justinjradi/smooth-scrolling-mouse/mouse-firmware-2/Core/Inc/board_api.h

/*
 * The MIT License (MIT)
 *
 * Copyright (c) 2019 Ha Thach (tinyusb.org)
 *
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
 * This file is part of the TinyUSB stack.
 */

#ifndef _BOARD_API_H_
#define _BOARD_API_H_

#ifdef __cplusplus
extern "C" {
#endif

#include <stdint.h>
#include <inttypes.h>
#include <stdbool.h>
#include <string.h>

#include "tusb.h"

#if CFG_TUSB_OS == OPT_OS_FREERTOS
#if TUP_MCU_ESPRESSIF
  // ESP-IDF need "freertos/" prefix in include path.
  // CFG_TUSB_OS_INC_PATH should be defined accordingly.
  #include "freertos/FreeRTOS.h"
  #include "freertos/semphr.h"
  #include "freertos/queue.h"
  #include "freertos/task.h"
  #include "freertos/timers.h"
#else
  #include "FreeRTOS.h"
  #include "semphr.h"
  #include "queue.h"
  #include "task.h"
  #include "timers.h"
#endif
#endif

// Define the default baudrate
#ifndef CFG_BOARD_UART_BAUDRATE
#define CFG_BOARD_UART_BAUDRATE 115200   ///< Default baud rate
#endif

//--------------------------------------------------------------------+
// Board Porting API
// For simplicity, only one LED and one Button are used
//--------------------------------------------------------------------+

// Get board unique ID for USB serial number. Return number of bytes. Note max_len is typically 16
TU_ATTR_WEAK size_t board_get_unique_id(uint8_t id[], size_t max_len);

// Send characters to UART. Return number of sent bytes
int board_uart_write(void const *buf, int len);

#if CFG_TUSB_OS == OPT_OS_NONE
// Get current milliseconds, must be implemented when no RTOS is used
uint32_t board_millis(void);

#elif CFG_TUSB_OS == OPT_OS_FREERTOS
static inline uint32_t board_millis(void) {
  return ( ( ((uint64_t) xTaskGetTickCount()) * 1000) / configTICK_RATE_HZ );
}

#elif CFG_TUSB_OS == OPT_OS_MYNEWT
static inline uint32_t board_millis(void) {
  return os_time_ticks_to_ms32( os_time_get() );
}

#elif CFG_TUSB_OS == OPT_OS_PICO
#include "pico/time.h"
static inline uint32_t board_millis(void) {
  return to_ms_since_boot(get_absolute_time());
}

#elif CFG_TUSB_OS == OPT_OS_RTTHREAD
static inline uint32_t board_millis(void) {
  return (((uint64_t)rt_tick_get()) * 1000 / RT_TICK_PER_SECOND);
}

#elif CFG_TUSB_OS == OPT_OS_CUSTOM
// Implement your own board_millis() in any of .c file
uint32_t board_millis(void);

#else
  #error "board_millis() is not implemented for this OS"
#endif

//--------------------------------------------------------------------+
// Helper functions
//--------------------------------------------------------------------+

// Get USB Serial number string from unique ID if available. Return number of character.
// Input is string descriptor from index 1 (index 0 is type + len)
static inline size_t board_usb_get_serial(uint16_t desc_str1[], size_t max_chars) {
  uint8_t uid[16] TU_ATTR_ALIGNED(4);
  size_t uid_len;

  // TODO work with make, but not working with esp32s3 cmake
  if ( board_get_unique_id ) {
    uid_len = board_get_unique_id(uid, sizeof(uid));
  }else {
    // fixed serial string is 01234567889ABCDEF
    uint32_t* uid32 = (uint32_t*) (uintptr_t) uid;
    uid32[0] = 0x67452301;
    uid32[1] = 0xEFCDAB89;
    uid_len = 8;
  }

  if ( uid_len > max_chars / 2 ) uid_len = max_chars / 2;

  for ( size_t i = 0; i < uid_len; i++ ) {
    for ( size_t j = 0; j < 2; j++ ) {
      const char nibble_to_hex[16] = {
          '0', '1', '2', '3', '4', '5', '6', '7',
          '8', '9', 'A', 'B', 'C', 'D', 'E', 'F'
      };
      uint8_t const nibble = (uid[i] >> (j * 4)) & 0xf;
      desc_str1[i * 2 + (1 - j)] = nibble_to_hex[nibble]; // UTF-16-LE
    }
  }

  return 2 * uid_len;
}

#ifdef __cplusplus
}
#endif

#endif
