justinjradi/smooth-scrolling-mouse/mouse-firmware-2/Core/Src/delay.c

/*
 * delay.c
 *
 *  Created on: Dec 19, 2025
 *      Based off code by Khaled Magdy
 */

#include "delay.h"

static int is_init = 0;

uint32_t delay_init(void)
{
    /* Disable TRC */
    CoreDebug->DEMCR &= ~CoreDebug_DEMCR_TRCENA_Msk; // ~0x01000000;
    /* Enable TRC */
    CoreDebug->DEMCR |=  CoreDebug_DEMCR_TRCENA_Msk; // 0x01000000;

    /* Disable clock cycle counter */
    DWT->CTRL &= ~DWT_CTRL_CYCCNTENA_Msk; //~0x00000001;
    /* Enable  clock cycle counter */
    DWT->CTRL |=  DWT_CTRL_CYCCNTENA_Msk; //0x00000001;

    /* Reset the clock cycle counter value */
    DWT->CYCCNT = 0;

    /* 3 NO OPERATION instructions */
    __ASM volatile ("NOP");
    __ASM volatile ("NOP");
    __ASM volatile ("NOP");

    /* Check if clock cycle counter has started */
    if(DWT->CYCCNT)
    {
    	is_init = 1;
    	return 0; /*clock cycle counter started*/
    }
    else
    {
      return 1; /*clock cycle counter not started*/
    }
}

// This Function Provides Delay In Microseconds Using DWT
void delay_us(volatile uint32_t au32_microseconds)
{
	if (is_init == 0)
	{
		delay_init();
		if (is_init == 0) return;
	}
  uint32_t au32_initial_ticks = DWT->CYCCNT;
  uint32_t au32_ticks = (HAL_RCC_GetHCLKFreq() / 1000000);
  au32_microseconds *= au32_ticks;
  while ((DWT->CYCCNT - au32_initial_ticks) < au32_microseconds-au32_ticks);
}

// This Function Provides Delay In Milliseconds Using DWT
void delay_ms(volatile uint32_t au32_milliseconds)
{
	if (is_init == 0)
	{
		delay_init();
		if (is_init == 0) return;
	}
  uint32_t au32_initial_ticks = DWT->CYCCNT;
  uint32_t au32_ticks = (HAL_RCC_GetHCLKFreq() / 1000);
  au32_milliseconds *= au32_ticks;
  while ((DWT->CYCCNT - au32_initial_ticks) < au32_milliseconds);
}
